MogleyC/BLEKeyboard20230211/Ses/BLEKeyboard/SRC/module_ble.c

#include "module_ble.h"
//#include <stdint.h>
#include <string.h>
//#include "ble.h"
//#include "ble_err.h"
//#include "ble_hci.h"
#include "ble_srv_common.h"
#include "ble_advertising.h"
//#include "ble_advdata.h"
#include "ble_hids.h"
#include "ble_bas.h"
#include "ble_dis.h"
#include "ble_conn_params.h"
#include "app_timer.h"
#include "peer_manager.h"
//#include "peer_manager_handler.h"
#include "nrf_sdh.h"
//#include "nrf_sdh_soc.h"
#include "nrf_sdh_ble.h"
#include "nrf_ble_gatt.h"
#include "nrf_ble_qwr.h"
#include "app_error.h"
#include "nrf_log.h"

#define DEVICE_NAME                         "Nordic_Keyboard"                          /**< Name of device. Will be included in the advertising data. */
#define MANUFACTURER_NAME                   "NordicSemiconductor"                      /**< Manufacturer. Will be passed to Device Information Service. */

#define APP_BLE_OBSERVER_PRIO               3                                          /**< Application's BLE observer priority. You shouldn't need to modify this value. */
#define APP_BLE_CONN_CFG_TAG                1                                          /**< A tag identifying the SoftDevice BLE configuration. */

#define PNP_ID_VENDOR_ID_SOURCE             0x02                                       /**< Vendor ID Source. */
#define PNP_ID_VENDOR_ID                    0x1915                                     /**< Vendor ID. */
#define PNP_ID_PRODUCT_ID                   0xEEEE                                     /**< Product ID. */
#define PNP_ID_PRODUCT_VERSION              0x0001                                     /**< Product Version. */

#define APP_ADV_FAST_INTERVAL               0x0028                                     /**< Fast advertising interval (in units of 0.625 ms. This value corresponds to 25 ms.). */
#define APP_ADV_SLOW_INTERVAL               0x0C80                                     /**< Slow advertising interval (in units of 0.625 ms. This value corrsponds to 2 seconds). */
#define APP_ADV_FAST_DURATION               3000                                       /**< The advertising duration of fast advertising in units of 10 milliseconds. */
#define APP_ADV_SLOW_DURATION               18000                                      /**< The advertising duration of slow advertising in units of 10 milliseconds. */

/*lint -emacro(524, MIN_CONN_INTERVAL) // Loss of precision */
#define MIN_CONN_INTERVAL                   MSEC_TO_UNITS(7.5, UNIT_1_25_MS)           /**< Minimum connection interval (7.5 ms) */
#define MAX_CONN_INTERVAL                   MSEC_TO_UNITS(30, UNIT_1_25_MS)            /**< Maximum connection interval (30 ms). */
#define SLAVE_LATENCY                       6                                          /**< Slave latency. */
#define CONN_SUP_TIMEOUT                    MSEC_TO_UNITS(430, UNIT_10_MS)             /**< Connection supervisory timeout (430 ms). */

#define FIRST_CONN_PARAMS_UPDATE_DELAY      APP_TIMER_TICKS(5000)                      /**< Time from initiating event (connect or start of notification) to first time sd_ble_gap_conn_param_update is called (5 seconds). */
#define NEXT_CONN_PARAMS_UPDATE_DELAY       APP_TIMER_TICKS(30000)                     /**< Time between each call to sd_ble_gap_conn_param_update after the first call (30 seconds). */
#define MAX_CONN_PARAMS_UPDATE_COUNT        3                                          /**< Number of attempts before giving up the connection parameter negotiation. */

#define SEC_PARAM_BOND                      1                                          /**< Perform bonding. */
#define SEC_PARAM_MITM                      0                                          /**< Man In The Middle protection not required. */
#define SEC_PARAM_LESC                      0                                          /**< LE Secure Connections not enabled. */
#define SEC_PARAM_KEYPRESS                  0                                          /**< Keypress notifications not enabled. */
#define SEC_PARAM_IO_CAPABILITIES           BLE_GAP_IO_CAPS_NONE                       /**< No I/O capabilities. */
#define SEC_PARAM_OOB                       0                                          /**< Out Of Band data not available. */
#define SEC_PARAM_MIN_KEY_SIZE              7                                          /**< Minimum encryption key size. */
#define SEC_PARAM_MAX_KEY_SIZE              16                                         /**< Maximum encryption key size. */

#define OUTPUT_REPORT_INDEX                 0                                          /**< Index of Output Report. */
#define OUTPUT_REPORT_MAX_LEN               1                                          /**< Maximum length of Output Report. */
#define INPUT_REPORT_KEYS_INDEX             0                                          /**< Index of Input Report. */
#define INPUT_REP_REF_ID                    0                                          /**< Id of reference to Keyboard Input Report. */
#define OUTPUT_REP_REF_ID                   0                                          /**< Id of reference to Keyboard Output Report. */
#define FEATURE_REP_REF_ID                  0                                          /**< ID of reference to Keyboard Feature Report. */
#define FEATURE_REPORT_MAX_LEN              2                                          /**< Maximum length of Feature Report. */
#define FEATURE_REPORT_INDEX                0                                          /**< Index of Feature Report. */

#define BASE_USB_HID_SPEC_VERSION           0x0101                                     /**< Version number of base USB HID Specification implemented by this application. */

#define INPUT_REPORT_KEYS_MAX_LEN           8                                          /**< Maximum length of the Input Report characteristic. */

BLE_HIDS_DEF(m_hids,                                                /**< Structure used to identify the HID service. */
             NRF_SDH_BLE_TOTAL_LINK_COUNT,
             INPUT_REPORT_KEYS_MAX_LEN,
             OUTPUT_REPORT_MAX_LEN,
             FEATURE_REPORT_MAX_LEN);
BLE_BAS_DEF(m_bas);                                                 /**< Structure used to identify the battery service. */
NRF_BLE_GATT_DEF(m_gatt);                                           /**< GATT module instance. */
NRF_BLE_QWR_DEF(m_qwr);                                             /**< Context for the Queued Write module.*/
BLE_ADVERTISING_DEF(m_advertising);                                 /**< Advertising module instance. */

static pm_peer_id_t      m_peer_id;                                 /**< Device reference handle to the current bonded central. */
static ble_uuid_t m_adv_uuids[] = {{BLE_UUID_HUMAN_INTERFACE_DEVICE_SERVICE, BLE_UUID_TYPE_BLE}};

static void qwr_init();
static void dis_init();
static void bas_init();
static void hids_init();

static void ble_evt_handler(ble_evt_t const * p_ble_evt, void * p_context);
static void on_adv_evt(ble_adv_evt_t ble_adv_evt);
static void on_hids_evt(ble_hids_t * p_hids, ble_hids_evt_t * p_evt);
static void pm_evt_handler(pm_evt_t const * p_evt);

static void delete_bonds();
static void whitelist_set(pm_peer_id_list_skip_t skip);

static void ble_advertising_error_handler(uint32_t nrf_error);
static void nrf_qwr_error_handler(uint32_t nrf_error);
static void service_error_handler(uint32_t nrf_error);
static void conn_params_error_handler(uint32_t nrf_error);

/**@brief Function for initializing the BLE stack.
 *
 * @details Initializes the SoftDevice and the BLE event interrupt.
 */
void ble_stack_init()
{
    ret_code_t err_code;

	//소프트 디바이스 활성화 확인
    err_code = nrf_sdh_enable_request();
    APP_ERROR_CHECK(err_code);

    // Configure the BLE stack using the default settings.
    // Fetch the start address of the application RAM.
    uint32_t ram_start = 0;
    err_code = nrf_sdh_ble_default_cfg_set(APP_BLE_CONN_CFG_TAG, &ram_start);
    APP_ERROR_CHECK(err_code);

    // Enable BLE stack.
    err_code = nrf_sdh_ble_enable(&ram_start);
    APP_ERROR_CHECK(err_code);

    // Register a handler for BLE events.
	// BLE 이벤트 발생시 콜백되는 메서드 등록
    NRF_SDH_BLE_OBSERVER(m_ble_observer, APP_BLE_OBSERVER_PRIO, ble_evt_handler, NULL);
}

/**@brief Function for the GAP initialization.
 *
 * @details This function sets up all the necessary GAP (Generic Access Profile) parameters of the
 *          device including the device name, appearance, and the preferred connection parameters.
 */
void gap_params_init()
{
    ret_code_t              err_code;
    ble_gap_conn_params_t   gap_conn_params;
    ble_gap_conn_sec_mode_t sec_mode;

    BLE_GAP_CONN_SEC_MODE_SET_OPEN(&sec_mode);

    err_code = sd_ble_gap_device_name_set(&sec_mode,
                                          (const uint8_t *)DEVICE_NAME,
                                          strlen(DEVICE_NAME));
    APP_ERROR_CHECK(err_code);

    err_code = sd_ble_gap_appearance_set(BLE_APPEARANCE_HID_KEYBOARD);
    APP_ERROR_CHECK(err_code);

    memset(&gap_conn_params, 0, sizeof(gap_conn_params));

    gap_conn_params.min_conn_interval = MIN_CONN_INTERVAL;
    gap_conn_params.max_conn_interval = MAX_CONN_INTERVAL;
    gap_conn_params.slave_latency     = SLAVE_LATENCY;
    gap_conn_params.conn_sup_timeout  = CONN_SUP_TIMEOUT;

    err_code = sd_ble_gap_ppcp_set(&gap_conn_params);
    APP_ERROR_CHECK(err_code);
}

/**@brief Function for initializing the GATT module.
 */
void gatt_init()
{
    ret_code_t err_code = nrf_ble_gatt_init(&m_gatt, NULL);
    APP_ERROR_CHECK(err_code);
}

/**@brief Function for initializing the Advertising functionality.
 */
void advertising_init()
{
    uint32_t               err_code;
    uint8_t                adv_flags;
    ble_advertising_init_t init;

    memset(&init, 0, sizeof(init));

    adv_flags                            = BLE_GAP_ADV_FLAGS_LE_ONLY_GENERAL_DISC_MODE;
    init.advdata.name_type               = BLE_ADVDATA_FULL_NAME;
    init.advdata.include_appearance      = true;
    init.advdata.flags                   = adv_flags;
    init.advdata.uuids_complete.uuid_cnt = sizeof(m_adv_uuids) / sizeof(m_adv_uuids[0]);
    init.advdata.uuids_complete.p_uuids  = m_adv_uuids;

    init.config.ble_adv_whitelist_enabled          = true;
    init.config.ble_adv_directed_high_duty_enabled = true;
    init.config.ble_adv_directed_enabled           = false;
    init.config.ble_adv_directed_interval          = 0;
    init.config.ble_adv_directed_timeout           = 0;
    init.config.ble_adv_fast_enabled               = true;
    init.config.ble_adv_fast_interval              = APP_ADV_FAST_INTERVAL;
    init.config.ble_adv_fast_timeout               = APP_ADV_FAST_DURATION;
    init.config.ble_adv_slow_enabled               = true;
    init.config.ble_adv_slow_interval              = APP_ADV_SLOW_INTERVAL;
    init.config.ble_adv_slow_timeout               = APP_ADV_SLOW_DURATION;

    init.evt_handler   = on_adv_evt;
    init.error_handler = ble_advertising_error_handler;

    err_code = ble_advertising_init(&m_advertising, &init);
    APP_ERROR_CHECK(err_code);

    ble_advertising_conn_cfg_tag_set(&m_advertising, APP_BLE_CONN_CFG_TAG);
}

/**@brief Function for initializing services that will be used by the application.
 */
void services_init()
{
	// Queued Writes module을 초기화 
	// 실질적으로는 여기서 BLE에 등록되지 않음
	// 여러개가 생성 가능한 것으로 보임
    qwr_init();
	// 디바이스 인포메이션 서비스
	// 여러개 생성 불가
    dis_init();
	// 배터리 서비스 
	// 여러개가 가능하지만 필요는 없다.
    bas_init();
	// HID 서비스
	// NRF_SDH_BLE_TOTAL_LINK_COUNT 를 수정 -> X
	// 여러개의 HID 서비스를 만들어야 한다.
	// 이것을 여러번 호출하면 각기 다른 UUID의 HID가 생성되는 것 같다.
    hids_init();
}

/**@brief Function for initializing the Queued Write Module.
 */
static void qwr_init()
{
    ret_code_t         err_code;
    nrf_ble_qwr_init_t qwr_init_obj = {0};

    qwr_init_obj.error_handler = nrf_qwr_error_handler;

    err_code = nrf_ble_qwr_init(&m_qwr, &qwr_init_obj);
    APP_ERROR_CHECK(err_code);
}


/**@brief Function for initializing Device Information Service.
 */
static void dis_init()
{
    ret_code_t       err_code;
    ble_dis_init_t   dis_init_obj;
    ble_dis_pnp_id_t pnp_id;

    pnp_id.vendor_id_source = PNP_ID_VENDOR_ID_SOURCE;
    pnp_id.vendor_id        = PNP_ID_VENDOR_ID;
    pnp_id.product_id       = PNP_ID_PRODUCT_ID;
    pnp_id.product_version  = PNP_ID_PRODUCT_VERSION;

    memset(&dis_init_obj, 0, sizeof(dis_init_obj));

    ble_srv_ascii_to_utf8(&dis_init_obj.manufact_name_str, MANUFACTURER_NAME);
    dis_init_obj.p_pnp_id = &pnp_id;

    dis_init_obj.dis_char_rd_sec = SEC_JUST_WORKS;

    err_code = ble_dis_init(&dis_init_obj);
    APP_ERROR_CHECK(err_code);
}


/**@brief Function for initializing Battery Service.
 */
static void bas_init()
{
    ret_code_t     err_code;
    ble_bas_init_t bas_init_obj;

    memset(&bas_init_obj, 0, sizeof(bas_init_obj));

    bas_init_obj.evt_handler          = NULL;
    bas_init_obj.support_notification = true;
    bas_init_obj.p_report_ref         = NULL;
    bas_init_obj.initial_batt_level   = 100;

    bas_init_obj.bl_rd_sec        = SEC_JUST_WORKS;
    bas_init_obj.bl_cccd_wr_sec   = SEC_JUST_WORKS;
    bas_init_obj.bl_report_rd_sec = SEC_JUST_WORKS;

    err_code = ble_bas_init(&m_bas, &bas_init_obj);
    APP_ERROR_CHECK(err_code);
}


/**@brief Function for initializing HID Service.
 */
static void hids_init()
{
    ret_code_t                    err_code;
    ble_hids_init_t               hids_init_obj;
    ble_hids_inp_rep_init_t     * p_input_report;
    ble_hids_outp_rep_init_t    * p_output_report;
    ble_hids_feature_rep_init_t * p_feature_report;
    uint8_t                       hid_info_flags;

    static ble_hids_inp_rep_init_t     input_report_array[1];
    static ble_hids_outp_rep_init_t    output_report_array[1];
    static ble_hids_feature_rep_init_t feature_report_array[1];
    static uint8_t                     report_map_data[] =
    {
        0x05, 0x01,       // Usage Page (Generic Desktop)
        0x09, 0x06,       // Usage (Keyboard)
        0xA1, 0x01,       // Collection (Application)
        0x05, 0x07,       // Usage Page (Key Codes)
        0x19, 0xe0,       // Usage Minimum (224)
        0x29, 0xe7,       // Usage Maximum (231)
        0x15, 0x00,       // Logical Minimum (0)
        0x25, 0x01,       // Logical Maximum (1)
        0x75, 0x01,       // Report Size (1)
        0x95, 0x08,       // Report Count (8)
        0x81, 0x02,       // Input (Data, Variable, Absolute)

        0x95, 0x01,       // Report Count (1)
        0x75, 0x08,       // Report Size (8)
        0x81, 0x01,       // Input (Constant) reserved byte(1)

        0x95, 0x05,       // Report Count (5)
        0x75, 0x01,       // Report Size (1)
        0x05, 0x08,       // Usage Page (Page# for LEDs)
        0x19, 0x01,       // Usage Minimum (1)
        0x29, 0x05,       // Usage Maximum (5)
        0x91, 0x02,       // Output (Data, Variable, Absolute), Led report
        0x95, 0x01,       // Report Count (1)
        0x75, 0x03,       // Report Size (3)
        0x91, 0x01,       // Output (Data, Variable, Absolute), Led report padding

        0x95, 0x06,       // Report Count (6)
        0x75, 0x08,       // Report Size (8)
        0x15, 0x00,       // Logical Minimum (0)
        0x25, 0x65,       // Logical Maximum (101)
        0x05, 0x07,       // Usage Page (Key codes)
        0x19, 0x00,       // Usage Minimum (0)
        0x29, 0x65,       // Usage Maximum (101)
        0x81, 0x00,       // Input (Data, Array) Key array(6 bytes)

        0x09, 0x05,       // Usage (Vendor Defined)
        0x15, 0x00,       // Logical Minimum (0)
        0x26, 0xFF, 0x00, // Logical Maximum (255)
        0x75, 0x08,       // Report Size (8 bit)
        0x95, 0x02,       // Report Count (2)
        0xB1, 0x02,       // Feature (Data, Variable, Absolute)

        0xC0              // End Collection (Application)
    };

    memset((void *)input_report_array, 0, sizeof(ble_hids_inp_rep_init_t));
    memset((void *)output_report_array, 0, sizeof(ble_hids_outp_rep_init_t));
    memset((void *)feature_report_array, 0, sizeof(ble_hids_feature_rep_init_t));

    // Initialize HID Service
    p_input_report                      = &input_report_array[INPUT_REPORT_KEYS_INDEX];
    p_input_report->max_len             = INPUT_REPORT_KEYS_MAX_LEN;
    p_input_report->rep_ref.report_id   = INPUT_REP_REF_ID;
    p_input_report->rep_ref.report_type = BLE_HIDS_REP_TYPE_INPUT;

    p_input_report->sec.cccd_wr = SEC_JUST_WORKS;
    p_input_report->sec.wr      = SEC_JUST_WORKS;
    p_input_report->sec.rd      = SEC_JUST_WORKS;

    p_output_report                      = &output_report_array[OUTPUT_REPORT_INDEX];
    p_output_report->max_len             = OUTPUT_REPORT_MAX_LEN;
    p_output_report->rep_ref.report_id   = OUTPUT_REP_REF_ID;
    p_output_report->rep_ref.report_type = BLE_HIDS_REP_TYPE_OUTPUT;

    p_output_report->sec.wr = SEC_JUST_WORKS;
    p_output_report->sec.rd = SEC_JUST_WORKS;

    p_feature_report                      = &feature_report_array[FEATURE_REPORT_INDEX];
    p_feature_report->max_len             = FEATURE_REPORT_MAX_LEN;
    p_feature_report->rep_ref.report_id   = FEATURE_REP_REF_ID;
    p_feature_report->rep_ref.report_type = BLE_HIDS_REP_TYPE_FEATURE;

    p_feature_report->sec.rd              = SEC_JUST_WORKS;
    p_feature_report->sec.wr              = SEC_JUST_WORKS;

    hid_info_flags = HID_INFO_FLAG_REMOTE_WAKE_MSK | HID_INFO_FLAG_NORMALLY_CONNECTABLE_MSK;

    memset(&hids_init_obj, 0, sizeof(hids_init_obj));

    hids_init_obj.evt_handler                    = on_hids_evt;
    hids_init_obj.error_handler                  = service_error_handler;
    hids_init_obj.is_kb                          = true;
    hids_init_obj.is_mouse                       = false;
    hids_init_obj.inp_rep_count                  = 1;
    hids_init_obj.p_inp_rep_array                = input_report_array;
    hids_init_obj.outp_rep_count                 = 1;
    hids_init_obj.p_outp_rep_array               = output_report_array;
    hids_init_obj.feature_rep_count              = 1;
    hids_init_obj.p_feature_rep_array            = feature_report_array;
    hids_init_obj.rep_map.data_len               = sizeof(report_map_data);
    hids_init_obj.rep_map.p_data                 = report_map_data;
    hids_init_obj.hid_information.bcd_hid        = BASE_USB_HID_SPEC_VERSION;
    hids_init_obj.hid_information.b_country_code = 0;
    hids_init_obj.hid_information.flags          = hid_info_flags;
    hids_init_obj.included_services_count        = 0;
    hids_init_obj.p_included_services_array      = NULL;

    hids_init_obj.rep_map.rd_sec         = SEC_JUST_WORKS;
    hids_init_obj.hid_information.rd_sec = SEC_JUST_WORKS;

    hids_init_obj.boot_kb_inp_rep_sec.cccd_wr = SEC_JUST_WORKS;
    hids_init_obj.boot_kb_inp_rep_sec.rd      = SEC_JUST_WORKS;

    hids_init_obj.boot_kb_outp_rep_sec.rd = SEC_JUST_WORKS;
    hids_init_obj.boot_kb_outp_rep_sec.wr = SEC_JUST_WORKS;

    hids_init_obj.protocol_mode_rd_sec = SEC_JUST_WORKS;
    hids_init_obj.protocol_mode_wr_sec = SEC_JUST_WORKS;
    hids_init_obj.ctrl_point_wr_sec    = SEC_JUST_WORKS;

    err_code = ble_hids_init(&m_hids, &hids_init_obj);
    APP_ERROR_CHECK(err_code);
}
	
/**@brief Function for initializing the Connection Parameters module.
 */
void conn_params_init()
{
    ret_code_t             err_code;
    ble_conn_params_init_t cp_init;

    memset(&cp_init, 0, sizeof(cp_init));

    cp_init.p_conn_params                  = NULL;
    cp_init.first_conn_params_update_delay = FIRST_CONN_PARAMS_UPDATE_DELAY;
    cp_init.next_conn_params_update_delay  = NEXT_CONN_PARAMS_UPDATE_DELAY;
    cp_init.max_conn_params_update_count   = MAX_CONN_PARAMS_UPDATE_COUNT;
    cp_init.start_on_notify_cccd_handle    = BLE_GATT_HANDLE_INVALID;
    cp_init.disconnect_on_fail             = false;
    cp_init.evt_handler                    = NULL;
    cp_init.error_handler                  = conn_params_error_handler;

    err_code = ble_conn_params_init(&cp_init);
    APP_ERROR_CHECK(err_code);
}


/**@brief Function for the Peer Manager initialization.
 */
void peer_manager_init()
{
    ble_gap_sec_params_t sec_param;
    ret_code_t           err_code;

    err_code = pm_init();
    APP_ERROR_CHECK(err_code);

    memset(&sec_param, 0, sizeof(ble_gap_sec_params_t));

    // Security parameters to be used for all security procedures.
    sec_param.bond           = SEC_PARAM_BOND;
    sec_param.mitm           = SEC_PARAM_MITM;
    sec_param.lesc           = SEC_PARAM_LESC;
    sec_param.keypress       = SEC_PARAM_KEYPRESS;
    sec_param.io_caps        = SEC_PARAM_IO_CAPABILITIES;
    sec_param.oob            = SEC_PARAM_OOB;
    sec_param.min_key_size   = SEC_PARAM_MIN_KEY_SIZE;
    sec_param.max_key_size   = SEC_PARAM_MAX_KEY_SIZE;
    sec_param.kdist_own.enc  = 1;
    sec_param.kdist_own.id   = 1;
    sec_param.kdist_peer.enc = 1;
    sec_param.kdist_peer.id  = 1;

    err_code = pm_sec_params_set(&sec_param);
    APP_ERROR_CHECK(err_code);

    err_code = pm_register(pm_evt_handler);
    APP_ERROR_CHECK(err_code);
}


/**@brief Function for starting advertising.
 */
void advertising_start(bool erase_bonds)
{
    if (erase_bonds == true)
    {
        delete_bonds();
        // Advertising is started by PM_EVT_PEERS_DELETE_SUCCEEDED event.
    }
    else
    {
        whitelist_set(PM_PEER_ID_LIST_SKIP_NO_ID_ADDR);

        ret_code_t ret = ble_advertising_start(&m_advertising, BLE_ADV_MODE_FAST);
        APP_ERROR_CHECK(ret);
    }
}

/**@brief Clear bond information from persistent storage.
 */
static void delete_bonds()
{
    ret_code_t err_code;

    NRF_LOG_INFO("Erase bonds!");

    err_code = pm_peers_delete();
    APP_ERROR_CHECK(err_code);
}

/**@brief Function for setting filtered whitelist.
 *
 * @param[in] skip  Filter passed to @ref pm_peer_id_list.
 */
static void whitelist_set(pm_peer_id_list_skip_t skip)
{
    pm_peer_id_t peer_ids[BLE_GAP_WHITELIST_ADDR_MAX_COUNT];
    uint32_t     peer_id_count = BLE_GAP_WHITELIST_ADDR_MAX_COUNT;

    ret_code_t err_code = pm_peer_id_list(peer_ids, &peer_id_count, PM_PEER_ID_INVALID, skip);
    APP_ERROR_CHECK(err_code);

    NRF_LOG_INFO("\tm_whitelist_peer_cnt %d, MAX_PEERS_WLIST %d",
                   peer_id_count + 1,
                   BLE_GAP_WHITELIST_ADDR_MAX_COUNT);

    err_code = pm_whitelist_set(peer_ids, peer_id_count);
    APP_ERROR_CHECK(err_code);
}

/**@brief Function for handling BLE events.
 *
 * @param[in]   p_ble_evt   Bluetooth stack event.
 * @param[in]   p_context   Unused.
 */
static void ble_evt_handler(ble_evt_t const * p_ble_evt, void * p_context)
{
   // ret_code_t err_code;

   // switch (p_ble_evt->header.evt_id)
   // {
   //     case BLE_GAP_EVT_CONNECTED:
   //         NRF_LOG_INFO("Connected");
			//// 보드에 LED On/Off - 삭제할것
   //         err_code = bsp_indication_set(BSP_INDICATE_CONNECTED);
   //         APP_ERROR_CHECK(err_code);
			
			////BLE Queued Writes module에 연결 핸들을 등록한다.
   //         m_conn_handle = p_ble_evt->evt.gap_evt.conn_handle;
   //         err_code = nrf_ble_qwr_conn_handle_assign(&m_qwr, m_conn_handle);
   //         APP_ERROR_CHECK(err_code);
   //         break;

   //     case BLE_GAP_EVT_DISCONNECTED:
   //         NRF_LOG_INFO("Disconnected");
   //         // Dequeue all keys without transmission.
			//// 예약된 키보드 발송을 모두 제거
   //         (void) buffer_dequeue(false);

   //         m_conn_handle = BLE_CONN_HANDLE_INVALID;

   //         // Reset m_caps_on variable. Upon reconnect, the HID host will re-send the Output
   //         // report containing the Caps lock state.
   //         m_caps_on = false;
			
   //         // disabling alert 3. signal - used for capslock ON
			//// 보드에 LED On/Off - 삭제할것
   //         err_code = bsp_indication_set(BSP_INDICATE_ALERT_OFF);
   //         APP_ERROR_CHECK(err_code);

   //         break; // BLE_GAP_EVT_DISCONNECTED

   //     case BLE_GAP_EVT_PHY_UPDATE_REQUEST:
   //     {
   //         NRF_LOG_DEBUG("PHY update request.");
   //         ble_gap_phys_t const phys =
   //         {
   //             .rx_phys = BLE_GAP_PHY_AUTO,
   //             .tx_phys = BLE_GAP_PHY_AUTO,
   //         };
   //         err_code = sd_ble_gap_phy_update(p_ble_evt->evt.gap_evt.conn_handle, &phys);
   //         APP_ERROR_CHECK(err_code);
   //     } break;

   //     case BLE_GATTS_EVT_HVN_TX_COMPLETE:
   //         // Send next key event
			//// 예약된 키를 발송한다. 이 예약은 한번에 많은 키를 발송할 때 HID한계에 의해 미처 다 발송하지 못할때 발생한다.
   //         (void) buffer_dequeue(true);
   //         break;

   //     case BLE_GATTC_EVT_TIMEOUT:
   //         // Disconnect on GATT Client timeout event.
   //         NRF_LOG_DEBUG("GATT Client Timeout.");
   //         err_code = sd_ble_gap_disconnect(p_ble_evt->evt.gattc_evt.conn_handle,
   //                                          BLE_HCI_REMOTE_USER_TERMINATED_CONNECTION);
   //         APP_ERROR_CHECK(err_code);
   //         break;

   //     case BLE_GATTS_EVT_TIMEOUT:
   //         // Disconnect on GATT Server timeout event.
   //         NRF_LOG_DEBUG("GATT Server Timeout.");
   //         err_code = sd_ble_gap_disconnect(p_ble_evt->evt.gatts_evt.conn_handle,
   //                                          BLE_HCI_REMOTE_USER_TERMINATED_CONNECTION);
   //         APP_ERROR_CHECK(err_code);
   //         break;

   //     default:
   //         // No implementation needed.
   //         break;
   // }
}

/**@brief Function for handling advertising events.
 *
 * @details This function will be called for advertising events which are passed to the application.
 *
 * @param[in] ble_adv_evt  Advertising event.
 */
static void on_adv_evt(ble_adv_evt_t ble_adv_evt)
{
    //ret_code_t err_code;

    //switch (ble_adv_evt)
    //{
    //    case BLE_ADV_EVT_DIRECTED_HIGH_DUTY:
    //        NRF_LOG_INFO("High Duty Directed advertising.");
    //        err_code = bsp_indication_set(BSP_INDICATE_ADVERTISING_DIRECTED);
    //        APP_ERROR_CHECK(err_code);
    //        break;

    //    case BLE_ADV_EVT_DIRECTED:
    //        NRF_LOG_INFO("Directed advertising.");
    //        err_code = bsp_indication_set(BSP_INDICATE_ADVERTISING_DIRECTED);
    //        APP_ERROR_CHECK(err_code);
    //        break;

    //    case BLE_ADV_EVT_FAST:
    //        NRF_LOG_INFO("Fast advertising.");
    //        err_code = bsp_indication_set(BSP_INDICATE_ADVERTISING);
    //        APP_ERROR_CHECK(err_code);
    //        break;

    //    case BLE_ADV_EVT_SLOW:
    //        NRF_LOG_INFO("Slow advertising.");
    //        err_code = bsp_indication_set(BSP_INDICATE_ADVERTISING_SLOW);
    //        APP_ERROR_CHECK(err_code);
    //        break;

    //    case BLE_ADV_EVT_FAST_WHITELIST:
    //        NRF_LOG_INFO("Fast advertising with whitelist.");
    //        err_code = bsp_indication_set(BSP_INDICATE_ADVERTISING_WHITELIST);
    //        APP_ERROR_CHECK(err_code);
    //        break;

    //    case BLE_ADV_EVT_SLOW_WHITELIST:
    //        NRF_LOG_INFO("Slow advertising with whitelist.");
    //        err_code = bsp_indication_set(BSP_INDICATE_ADVERTISING_WHITELIST);
    //        APP_ERROR_CHECK(err_code);
    //        break;

    //    case BLE_ADV_EVT_IDLE:
    //        sleep_mode_enter();
    //        break;

    //    case BLE_ADV_EVT_WHITELIST_REQUEST:
    //    {
    //        ble_gap_addr_t whitelist_addrs[BLE_GAP_WHITELIST_ADDR_MAX_COUNT];
    //        ble_gap_irk_t  whitelist_irks[BLE_GAP_WHITELIST_ADDR_MAX_COUNT];
    //        uint32_t       addr_cnt = BLE_GAP_WHITELIST_ADDR_MAX_COUNT;
    //        uint32_t       irk_cnt  = BLE_GAP_WHITELIST_ADDR_MAX_COUNT;

    //        err_code = pm_whitelist_get(whitelist_addrs, &addr_cnt,
    //                                    whitelist_irks,  &irk_cnt);
    //        APP_ERROR_CHECK(err_code);
    //        NRF_LOG_DEBUG("pm_whitelist_get returns %d addr in whitelist and %d irk whitelist",
    //                      addr_cnt, irk_cnt);

    //        // Set the correct identities list (no excluding peers with no Central Address Resolution).
    //        identities_set(PM_PEER_ID_LIST_SKIP_NO_IRK);

    //        // Apply the whitelist.
    //        err_code = ble_advertising_whitelist_reply(&m_advertising,
    //                                                   whitelist_addrs,
    //                                                   addr_cnt,
    //                                                   whitelist_irks,
    //                                                   irk_cnt);
    //        APP_ERROR_CHECK(err_code);
    //    } break; //BLE_ADV_EVT_WHITELIST_REQUEST

    //    case BLE_ADV_EVT_PEER_ADDR_REQUEST:
    //    {
    //        pm_peer_data_bonding_t peer_bonding_data;

    //        // Only Give peer address if we have a handle to the bonded peer.
    //        if (m_peer_id != PM_PEER_ID_INVALID)
    //        {
    //            err_code = pm_peer_data_bonding_load(m_peer_id, &peer_bonding_data);
    //            if (err_code != NRF_ERROR_NOT_FOUND)
    //            {
    //                APP_ERROR_CHECK(err_code);

    //                // Manipulate identities to exclude peers with no Central Address Resolution.
    //                identities_set(PM_PEER_ID_LIST_SKIP_ALL);

    //                ble_gap_addr_t * p_peer_addr = &(peer_bonding_data.peer_ble_id.id_addr_info);
    //                err_code = ble_advertising_peer_addr_reply(&m_advertising, p_peer_addr);
    //                APP_ERROR_CHECK(err_code);
    //            }
    //        }
    //    } break; //BLE_ADV_EVT_PEER_ADDR_REQUEST

    //    default:
    //        break;
    //}
}

/**@brief Function for handling HID events.
 *
 * @details This function will be called for all HID events which are passed to the application.
 *
 * @param[in]   p_hids  HID service structure.
 * @param[in]   p_evt   Event received from the HID service.
 */
static void on_hids_evt(ble_hids_t * p_hids, ble_hids_evt_t * p_evt)
{
	//// HiD이벤트가 발생될때 호출된다.
	//// ble_hids의 p_hids->evt_handler에 연결되어 여러 부분에서 호출된다.
 //   switch (p_evt->evt_type)
 //   {
 //       case BLE_HIDS_EVT_BOOT_MODE_ENTERED:
 //           m_in_boot_mode = true;
 //           break;

 //       case BLE_HIDS_EVT_REPORT_MODE_ENTERED:
 //           m_in_boot_mode = false;
 //           break;

 //       case BLE_HIDS_EVT_REP_CHAR_WRITE:
 //           on_hid_rep_char_write(p_evt);
 //           break;

 //       case BLE_HIDS_EVT_NOTIF_ENABLED:
 //           break;

 //       default:
 //           // No implementation needed.
 //           break;
 //   }
}

/**@brief Function for handling Peer Manager events.
 *
 * @param[in] p_evt  Peer Manager event.
 */
static void pm_evt_handler(pm_evt_t const * p_evt)
{
    //pm_handler_on_pm_evt(p_evt);
    //pm_handler_disconnect_on_sec_failure(p_evt);
    //pm_handler_flash_clean(p_evt);

    //switch (p_evt->evt_id)
    //{
    //    case PM_EVT_CONN_SEC_SUCCEEDED:
    //        m_peer_id = p_evt->peer_id;
    //        break;

    //    case PM_EVT_PEERS_DELETE_SUCCEEDED:
    //        advertising_start(false);
    //        break;

    //    case PM_EVT_PEER_DATA_UPDATE_SUCCEEDED:
    //        if (     p_evt->params.peer_data_update_succeeded.flash_changed
    //             && (p_evt->params.peer_data_update_succeeded.data_id == PM_PEER_DATA_ID_BONDING))
    //        {
    //            NRF_LOG_INFO("New Bond, add the peer to the whitelist if possible");
    //            // Note: You should check on what kind of white list policy your application should use.

    //            whitelist_set(PM_PEER_ID_LIST_SKIP_NO_ID_ADDR);
    //        }
    //        break;

    //    default:
    //        break;
    //}
}

/**@brief Function for handling advertising errors.
 *
 * @param[in] nrf_error  Error code containing information about what went wrong.
 */
static void ble_advertising_error_handler(uint32_t nrf_error)
{
    APP_ERROR_HANDLER(nrf_error);
}

/**@brief Function for handling Queued Write Module errors.
 *
 * @details A pointer to this function will be passed to each service which may need to inform the
 *          application about an error.
 *
 * @param[in]   nrf_error   Error code containing information about what went wrong.
 */
static void nrf_qwr_error_handler(uint32_t nrf_error)
{
    APP_ERROR_HANDLER(nrf_error);
}


/**@brief Function for handling Service errors.
 *
 * @details A pointer to this function will be passed to each service which may need to inform the
 *          application about an error.
 *
 * @param[in]   nrf_error   Error code containing information about what went wrong.
 */
static void service_error_handler(uint32_t nrf_error)
{
    APP_ERROR_HANDLER(nrf_error);
}


/**@brief Function for handling a Connection Parameters error.
 *
 * @param[in]   nrf_error   Error code containing information about what went wrong.
 */
static void conn_params_error_handler(uint32_t nrf_error)
{
    APP_ERROR_HANDLER(nrf_error);
}
