MogleyC/BLEKeyboard20230211/VSCode/BLEKeyboard/src/hid_usages.h

/**
 * @file hid_usages.h
 * @author Kang Shin Gu (indra1469@naver.com)
 * @brief HID Keyboard Usages
 * 
 * check HID Usage Tables.
 * https://usb.org/document-library/hid-usage-tables-15
 * 
 * @version 1.0
 * @date 2024-05-25
 * 
 * @copyright Copyright (c) 2024
 * 
 */

#ifndef HID_USAGES_H
#define HID_USAGES_H

#define HID_KEY_MOD_LCTRL  0x01
#define HID_KEY_MOD_LSHIFT 0x02
#define HID_KEY_MOD_LALT   0x04
#define HID_KEY_MOD_LMETA  0x08
#define HID_KEY_MOD_RCTRL  0x10
#define HID_KEY_MOD_RSHIFT 0x20
#define HID_KEY_MOD_RALT   0x40
#define HID_KEY_MOD_RMETA  0x80

/**
 * Scan codes - last N slots in the HID report (usually 6).
 * 0x00 if no key pressed.
 * 
 * If more than N keys are pressed, the HID reports 
 * KEY_ERR_OVF in all slots to indicate this condition.
 */

#define HID_KEY_NONE 0x00 // No key pressed
#define HID_KEY_ERR_OVF 0x01 //  Keyboard Error Roll Over - used for all slots if too many keys are pressed ("Phantom key")
// 0x02 //  Keyboard POST Fail
// 0x03 //  Keyboard Error Undefined
#define HID_KEY_A 0x04 // Keyboard a and A
#define HID_KEY_B 0x05 // Keyboard b and B
#define HID_KEY_C 0x06 // Keyboard c and C
#define HID_KEY_D 0x07 // Keyboard d and D
#define HID_KEY_E 0x08 // Keyboard e and E
#define HID_KEY_F 0x09 // Keyboard f and F
#define HID_KEY_G 0x0a // Keyboard g and G
#define HID_KEY_H 0x0b // Keyboard h and H
#define HID_KEY_I 0x0c // Keyboard i and I
#define HID_KEY_J 0x0d // Keyboard j and J
#define HID_KEY_K 0x0e // Keyboard k and K
#define HID_KEY_L 0x0f // Keyboard l and L
#define HID_KEY_M 0x10 // Keyboard m and M
#define HID_KEY_N 0x11 // Keyboard n and N
#define HID_KEY_O 0x12 // Keyboard o and O
#define HID_KEY_P 0x13 // Keyboard p and P
#define HID_KEY_Q 0x14 // Keyboard q and Q
#define HID_KEY_R 0x15 // Keyboard r and R
#define HID_KEY_S 0x16 // Keyboard s and S
#define HID_KEY_T 0x17 // Keyboard t and T
#define HID_KEY_U 0x18 // Keyboard u and U
#define HID_KEY_V 0x19 // Keyboard v and V
#define HID_KEY_W 0x1a // Keyboard w and W
#define HID_KEY_X 0x1b // Keyboard x and X
#define HID_KEY_Y 0x1c // Keyboard y and Y
#define HID_KEY_Z 0x1d // Keyboard z and Z

#define HID_KEY_1 0x1e // Keyboard 1 and !
#define HID_KEY_2 0x1f // Keyboard 2 and @
#define HID_KEY_3 0x20 // Keyboard 3 and #
#define HID_KEY_4 0x21 // Keyboard 4 and $
#define HID_KEY_5 0x22 // Keyboard 5 and %
#define HID_KEY_6 0x23 // Keyboard 6 and ^
#define HID_KEY_7 0x24 // Keyboard 7 and &
#define HID_KEY_8 0x25 // Keyboard 8 and *
#define HID_KEY_9 0x26 // Keyboard 9 and (
#define HID_KEY_0 0x27 // Keyboard 0 and )

#define HID_KEY_ENTER 0x28 // Keyboard Return (ENTER)
#define HID_KEY_ESC 0x29 // Keyboard ESCAPE
#define HID_KEY_BACKSPACE 0x2a // Keyboard DELETE (Backspace)
#define HID_KEY_TAB 0x2b // Keyboard Tab
#define HID_KEY_SPACE 0x2c // Keyboard Spacebar
#define HID_KEY_MINUS 0x2d // Keyboard - and _
#define HID_KEY_EQUAL 0x2e // Keyboard = and +
#define HID_KEY_LEFTBRACE 0x2f // Keyboard [ and {
#define HID_KEY_RIGHTBRACE 0x30 // Keyboard ] and }
#define HID_KEY_BACKSLASH 0x31 // Keyboard \ and |
#define HID_KEY_HASHTILDE 0x32 // Keyboard Non-US # and ~
#define HID_KEY_SEMICOLON 0x33 // Keyboard ; and :
#define HID_KEY_APOSTROPHE 0x34 // Keyboard ' and "
#define HID_KEY_GRAVE 0x35 // Keyboard ` and ~
#define HID_KEY_COMMA 0x36 // Keyboard , and <
#define HID_KEY_DOT 0x37 // Keyboard . and >
#define HID_KEY_SLASH 0x38 // Keyboard / and ?
#define HID_KEY_CAPSLOCK 0x39 // Keyboard Caps Lock

#define HID_KEY_F1 0x3a // Keyboard F1
#define HID_KEY_F2 0x3b // Keyboard F2
#define HID_KEY_F3 0x3c // Keyboard F3
#define HID_KEY_F4 0x3d // Keyboard F4
#define HID_KEY_F5 0x3e // Keyboard F5
#define HID_KEY_F6 0x3f // Keyboard F6
#define HID_KEY_F7 0x40 // Keyboard F7
#define HID_KEY_F8 0x41 // Keyboard F8
#define HID_KEY_F9 0x42 // Keyboard F9
#define HID_KEY_F10 0x43 // Keyboard F10
#define HID_KEY_F11 0x44 // Keyboard F11
#define HID_KEY_F12 0x45 // Keyboard F12

#define HID_KEY_SYSRQ 0x46 // Keyboard Print Screen
#define HID_KEY_SCROLLLOCK 0x47 // Keyboard Scroll Lock
#define HID_KEY_PAUSE 0x48 // Keyboard Pause
#define HID_KEY_INSERT 0x49 // Keyboard Insert
#define HID_KEY_HOME 0x4a // Keyboard Home
#define HID_KEY_PAGEUP 0x4b // Keyboard Page Up
#define HID_KEY_DELETE 0x4c // Keyboard Delete Forward
#define HID_KEY_END 0x4d // Keyboard End
#define HID_KEY_PAGEDOWN 0x4e // Keyboard Page Down
#define HID_KEY_RIGHT 0x4f // Keyboard Right Arrow
#define HID_KEY_LEFT 0x50 // Keyboard Left Arrow
#define HID_KEY_DOWN 0x51 // Keyboard Down Arrow
#define HID_KEY_UP 0x52 // Keyboard Up Arrow

#define HID_KEY_NUMLOCK 0x53 // Keyboard Num Lock and Clear
#define HID_KEY_KPSLASH 0x54 // Keypad /
#define HID_KEY_KPASTERISK 0x55 // Keypad *
#define HID_KEY_KPMINUS 0x56 // Keypad -
#define HID_KEY_KPPLUS 0x57 // Keypad +
#define HID_KEY_KPENTER 0x58 // Keypad ENTER
#define HID_KEY_KP1 0x59 // Keypad 1 and End
#define HID_KEY_KP2 0x5a // Keypad 2 and Down Arrow
#define HID_KEY_KP3 0x5b // Keypad 3 and PageDn
#define HID_KEY_KP4 0x5c // Keypad 4 and Left Arrow
#define HID_KEY_KP5 0x5d // Keypad 5
#define HID_KEY_KP6 0x5e // Keypad 6 and Right Arrow
#define HID_KEY_KP7 0x5f // Keypad 7 and Home
#define HID_KEY_KP8 0x60 // Keypad 8 and Up Arrow
#define HID_KEY_KP9 0x61 // Keypad 9 and Page Up
#define HID_KEY_KP0 0x62 // Keypad 0 and Insert
#define HID_KEY_KPDOT 0x63 // Keypad . and Delete

#define HID_KEY_102ND 0x64 // Keyboard Non-US \ and |
#define HID_KEY_COMPOSE 0x65 // Keyboard Application
#define HID_KEY_POWER 0x66 // Keyboard Power
#define HID_KEY_KPEQUAL 0x67 // Keypad =

#define HID_KEY_F13 0x68 // Keyboard F13
#define HID_KEY_F14 0x69 // Keyboard F14
#define HID_KEY_F15 0x6a // Keyboard F15
#define HID_KEY_F16 0x6b // Keyboard F16
#define HID_KEY_F17 0x6c // Keyboard F17
#define HID_KEY_F18 0x6d // Keyboard F18
#define HID_KEY_F19 0x6e // Keyboard F19
#define HID_KEY_F20 0x6f // Keyboard F20
#define HID_KEY_F21 0x70 // Keyboard F21
#define HID_KEY_F22 0x71 // Keyboard F22
#define HID_KEY_F23 0x72 // Keyboard F23
#define HID_KEY_F24 0x73 // Keyboard F24

#define HID_KEY_OPEN 0x74 // Keyboard Execute
#define HID_KEY_HELP 0x75 // Keyboard Help
#define HID_KEY_PROPS 0x76 // Keyboard Menu
#define HID_KEY_FRONT 0x77 // Keyboard Select
#define HID_KEY_STOP 0x78 // Keyboard Stop
#define HID_KEY_AGAIN 0x79 // Keyboard Again
#define HID_KEY_UNDO 0x7a // Keyboard Undo
#define HID_KEY_CUT 0x7b // Keyboard Cut
#define HID_KEY_COPY 0x7c // Keyboard Copy
#define HID_KEY_PASTE 0x7d // Keyboard Paste
#define HID_KEY_FIND 0x7e // Keyboard Find
#define HID_KEY_MUTE 0x7f // Keyboard Mute
#define HID_KEY_VOLUMEUP 0x80 // Keyboard Volume Up
#define HID_KEY_VOLUMEDOWN 0x81 // Keyboard Volume Down
// 0x82  Keyboard Locking Caps Lock
// 0x83  Keyboard Locking Num Lock
// 0x84  Keyboard Locking Scroll Lock
#define HID_KEY_KPCOMMA 0x85 // Keypad Comma
// 0x86  Keypad Equal Sign
#define HID_KEY_RO 0x87 // Keyboard International1
#define HID_KEY_KATAKANAHIRAGANA 0x88 // Keyboard International2
#define HID_KEY_YEN 0x89 // Keyboard International3
#define HID_KEY_HENKAN 0x8a // Keyboard International4
#define HID_KEY_MUHENKAN 0x8b // Keyboard International5
#define HID_KEY_KPJPCOMMA 0x8c // Keyboard International6
// 0x8d  Keyboard International7
// 0x8e  Keyboard International8
// 0x8f  Keyboard International9
#define HID_KEY_HANGEUL 0x90 // Keyboard LANG1
#define HID_KEY_HANJA 0x91 // Keyboard LANG2
#define HID_KEY_KATAKANA 0x92 // Keyboard LANG3
#define HID_KEY_HIRAGANA 0x93 // Keyboard LANG4
#define HID_KEY_ZENKAKUHANKAKU 0x94 // Keyboard LANG5

#define HID_KEY_KPLEFTPAREN 0xb6 // Keypad (
#define HID_KEY_KPRIGHTPAREN 0xb7 // Keypad )


#define HID_KEY_LEFTCTRL 0xe0 // Keyboard Left Control
#define HID_KEY_LEFTSHIFT 0xe1 // Keyboard Left Shift
#define HID_KEY_LEFTALT 0xe2 // Keyboard Left Alt
#define HID_KEY_LEFTMETA 0xe3 // Keyboard Left GUI
#define HID_KEY_RIGHTCTRL 0xe4 // Keyboard Right Control
#define HID_KEY_RIGHTSHIFT 0xe5 // Keyboard Right Shift
#define HID_KEY_RIGHTALT 0xe6 // Keyboard Right Alt
#define HID_KEY_RIGHTMETA 0xe7 // Keyboard Right GUI

#define HID_KEY_MEDIA_PLAYPAUSE 0xe8
#define HID_KEY_MEDIA_STOPCD 0xe9
#define HID_KEY_MEDIA_PREVIOUSSONG 0xea
#define HID_KEY_MEDIA_NEXTSONG 0xeb
#define HID_KEY_MEDIA_EJECTCD 0xec
#define HID_KEY_MEDIA_VOLUMEUP 0xed
#define HID_KEY_MEDIA_VOLUMEDOWN 0xee
#define HID_KEY_MEDIA_MUTE 0xef
#define HID_KEY_MEDIA_WWW 0xf0
#define HID_KEY_MEDIA_BACK 0xf1
#define HID_KEY_MEDIA_FORWARD 0xf2
#define HID_KEY_MEDIA_STOP 0xf3
#define HID_KEY_MEDIA_FIND 0xf4
#define HID_KEY_MEDIA_SCROLLUP 0xf5
#define HID_KEY_MEDIA_SCROLLDOWN 0xf6
#define HID_KEY_MEDIA_EDIT 0xf7
#define HID_KEY_MEDIA_SLEEP 0xf8
#define HID_KEY_MEDIA_COFFEE 0xf9
#define HID_KEY_MEDIA_REFRESH 0xfa
#define HID_KEY_MEDIA_CALC 0xfb

#endif
