MogleyC/BLEKeyboard20230211/VSCode/BLEKeyboard/src/gpio.h

#ifndef GPIO_H
#define GPIO_H

#include "include.h"

#include <zephyr/drivers/gpio.h>

struct key_status_msg_data_t
{
	uint8_t rowIdx;
	bool colKeyInput[4];
}typedef key_status_msg_data;

enum LEDstatus_e
{
	LEDstatus_isOff = 0,
	LEDstatus_isOn,
	LEDstatus_isBlink,
} typedef LEDstatus;


int gpio_init(void);
int gpio_thread_start(void);
struct k_msgq *get_key_status_msg_queue_ptr();
int gpio_setStatusLed(LEDstatus set);

#endif
