MogleyC/BLEKeyboard20230211/Ses/BLEKeyboard/SRC/module_app_scheduler.c

#include "module_app_scheduler.h"
//#include <stdint.h>
#include "app_scheduler.h"
#include "app_timer.h"

#define SCHED_MAX_EVENT_DATA_SIZE           APP_TIMER_SCHED_EVENT_DATA_SIZE            /**< Maximum size of scheduler events. */
#ifdef SVCALL_AS_NORMAL_FUNCTION
#define SCHED_QUEUE_SIZE                    20                                         /**< Maximum number of events in the scheduler queue. More is needed in case of Serialization. */
#else
#define SCHED_QUEUE_SIZE                    10                                         /**< Maximum number of events in the scheduler queue. */
#endif

/**@brief Function for the Event Scheduler initialization.
 */
void scheduler_init()
{
    APP_SCHED_INIT(SCHED_MAX_EVENT_DATA_SIZE, SCHED_QUEUE_SIZE);
}
