MogleyC/BLEKeyboard20230211/Ses/BLEKeyboard/SRC/module_nrf_log.c

#include "module_nrf_log.h"
//#include <stdint.h>
#include "nrf_log.h"
#include "nrf_log_ctrl.h"
#include "nrf_log_default_backends.h"

/**@brief Function for initializing the nrf log module.
 */
void log_init()
{
    ret_code_t err_code = NRF_LOG_INIT(NULL);
    APP_ERROR_CHECK(err_code);

    NRF_LOG_DEFAULT_BACKENDS_INIT();
}
